stbuccia/amarelli-backup/report/slides/img/topper.jpg

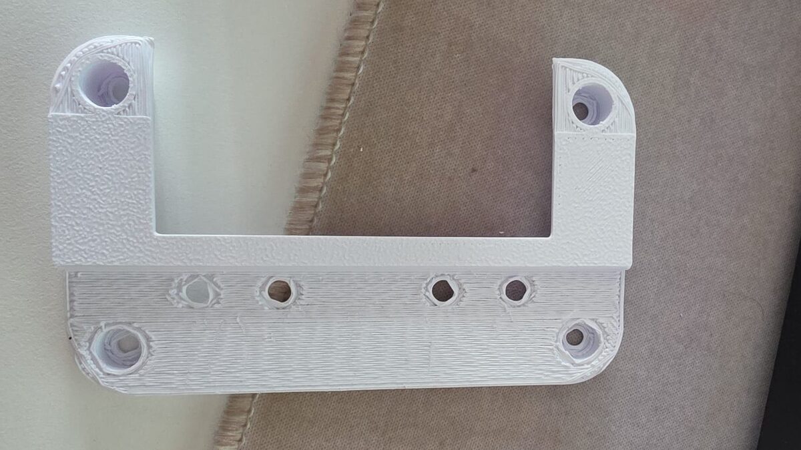
report/slides/img/topper.jpg
