stbuccia/amarelli-backup/report/slides/img/partlist-grid.png

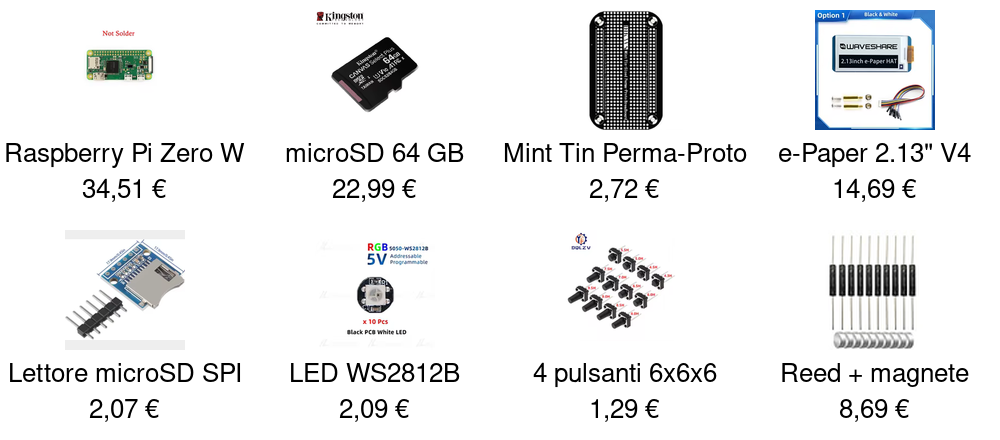
report/slides/img/partlist-grid.png
